Pippadi/combadge/hardware/pcb/assets/PCBFront.png

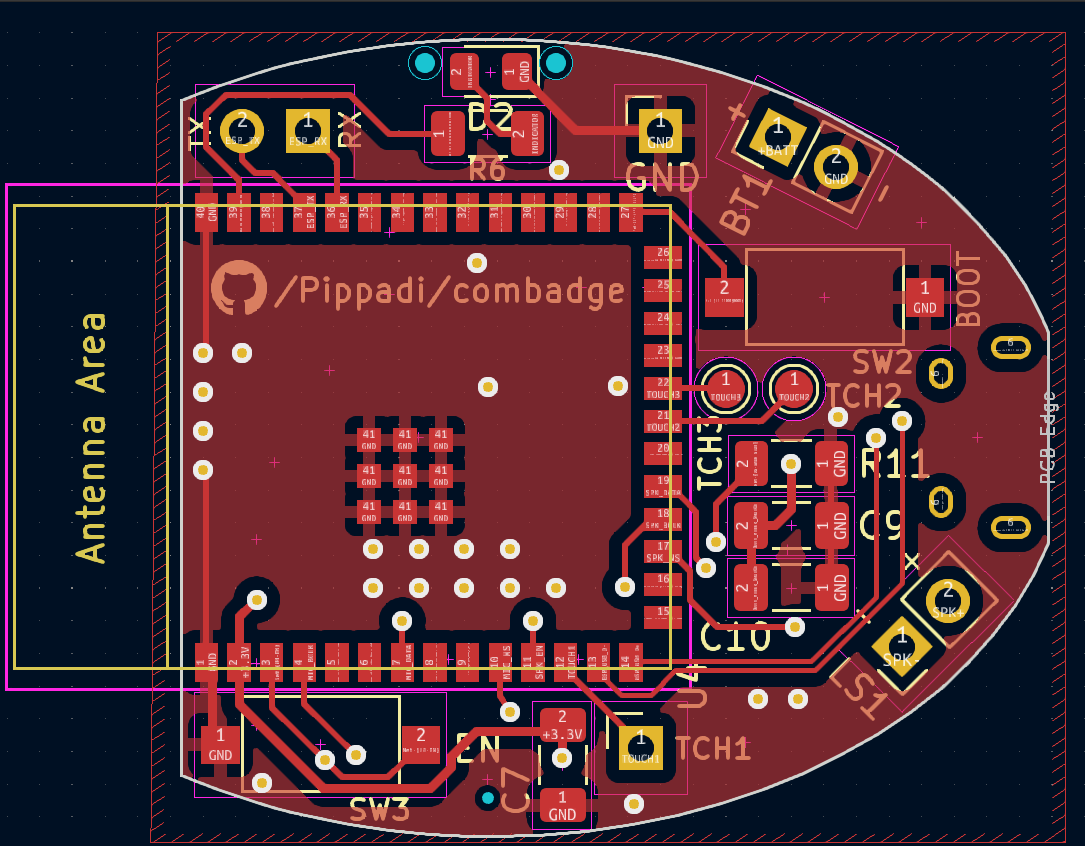
hardware/pcb/assets/PCBFront.png
