Pippadi/combadge/software/combadge/components/i2speripherals/i2scfg.hpp

#include <driver/i2s_std.h>

#ifndef I2SCfg_h
#define I2SCfg_h

struct I2SCfg {
    uint32_t sampleRate;
    int bitsPerSample;
};

struct MicPinCfg {
    gpio_num_t bclk;
    gpio_num_t ws;
    gpio_num_t data;
};

#endif
