Pippadi/combadge/software/combadge/components/i2speripherals/sph0645.hpp

#include <driver/i2s_std.h>
#include "i2scfg.hpp"

#ifndef SPH0645_h
#define SPH0645_h

class SPH0645 {
private:
    i2s_chan_handle_t chanHandle;

public:
    SPH0645();
    bool begin(i2s_port_t port, I2SCfg _cfg, MicPinCfg _pins);
    size_t read(int16_t* destination, size_t sampleCnt);
};

#endif
