Pippadi/combadge/software/test/playSound/TNGChirp1.h

const PROGMEM int16_t TNGChirp1[] = {
0xffff, 
0x0002, 0xfffd, 0x0004, 0xfffc, 0x0003, 0xfffe, 0x0001, 0x0000, 
0xffff, 0x0001, 0xffff, 0x0001, 0xffff, 0x0001, 0xfffe, 0x0003, 
0xfffc, 0x0005, 0xfffb, 0x0004, 0xfffd, 0x0001, 0x0002, 0xfffd, 
0x0003, 0xfffd, 0x0002, 0xfffe, 0x0002, 0xffff, 0x0001, 0x0000, 
0xfffe, 0x0002, 0xfffe, 0x0003, 0xfffe, 0x0001, 0xffff, 0x0001, 
0xffff, 0x0002, 0xfffe, 0x0001, 0x0000, 0xfffe, 0x0004, 0xfffc, 
0x0004, 0xfffc, 0x0003, 0xfffe, 0x0001, 0x0000, 0x0000, 0xffff, 
0x0002, 0xfffd, 0x0003, 0xfffd, 0x0002, 0xffff, 0x0000, 0x0001, 
0xffff, 0x0000, 0x0000, 0x0000, 0x0001, 0xffff, 0x0001, 0xffff, 
0x0000, 0x0001, 0xffff, 0x0001, 0x0000, 0xffff, 0x0002, 0xfffd, 
0x0003, 0xfffe, 0x0001, 0x0000, 0xffff, 0x0001, 0xffff, 0x0002, 
0xfffd, 0x0002, 0xffff, 0x0001, 0xffff, 0x0000, 0x0000, 0x0001, 
0xffff, 0x0000, 0x0000, 0xffff, 0x0003, 0xfffc, 0x0004, 0xfffd, 
0x0002, 0xfffe, 0x0003, 0xfffd, 0x0002, 0xffff, 0x0000, 0x0001, 
0xffff, 0x0000, 0x0001, 0xffff, 0x0000, 0x0001, 0xfffe, 0x0003, 
0xfffd, 0x0002, 0xffff, 0x0000, 0x0000, 0x0001, 0xffff, 0x0000, 
0x0001, 0xfffd, 0x0005, 0xfffb, 0x0004, 0xfffd, 0x0002, 0xffff, 
0x0000, 0x0001, 0xffff, 0x0001, 0xffff, 0x0001, 0xffff, 0x0001, 
0x0000, 0xffff, 0x0001, 0x0000, 0xffff, 0x0002, 0xfffe, 0x0000, 
0x0001, 0x0000, 0x0000, 0x0000, 0xfffe, 0x0002, 0x0000, 0x0000, 
0x0000, 0xffff, 0x0001, 0x0000, 0x0000, 0xffff, 0x0003, 0xfffb, 
0x0005, 0xfffc, 0x0002, 0x0001, 0xfffc, 0x0005, 0xfffc, 0x0002, 
0x0000, 0xfffe, 0x0003, 0xfffd, 0x0003, 0xfffd, 0x0003, 0xfffd, 
0x0002, 0xffff, 0x0000, 0x0001, 0xffff, 0x0000, 0x0001, 0xffff, 
0x0000, 0x0001, 0xfffe, 0x0003, 0xfffd, 0x0002, 0xffff, 0x0000, 
0x0002, 0xfffc, 0x0004, 0xfffd, 0x0002, 0xffff, 0x0000, 0x0000, 
0x0001, 0xfffe, 0x0002, 0xfffe, 0x0002, 0xfffe, 0x0002, 0xfffd, 
0x0003, 0xfffe, 0x0001, 0x0000, 0xfffe, 0x0003, 0xfffd, 0x0003, 
0xfffe, 0x0000, 0x0002, 0xfffd, 0x0004, 0xfffc, 0x0003, 0xfffe, 
0x0002, 0xfffe, 0x0002, 0xfffe, 0x0001, 0x0000, 0xffff, 0x0002, 
0xfffe, 0x0002, 0xfffe, 0x0001, 0x0000, 0x0000, 0x0000, 0x0000, 
0x0000, 0x0000, 0x0000, 0x0000, 0x0000, 0x0000, 0xffff, 0x0002, 
0xfffd, 0x0004, 0xfffc, 0x0003, 0xfffe, 0x0001, 0xffff, 0x0001, 
0x0000, 0xffff, 0x0002, 0xfffe, 0x0001, 0x0000, 0x0000, 0x0000, 
0x0000, 0x0001, 0xfffe, 0x0002, 0xffff, 0xffff, 0x0003, 0xfffc, 
0x0003, 0xffff, 0x0000, 0x0000, 0x0000, 0x0000, 0x0000, 0x0001, 
0xfffe, 0x0002, 0xfffe, 0x0002, 0xfffe, 0x0002, 0xfffe, 0x0002, 
0xfffe, 0x0002, 0xfffe, 0x0001, 0x0000, 0x0000, 0x0000, 0x0000, 
0x0000, 0xffff, 0x0002, 0xfffe, 0x0001, 0x0000, 0xffff, 0x0002, 
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
};

const size_t TNGChirp1SizeBytes = sizeof(TNGChirp1);
